hernss/switching_power_supply/TPS54331-KiCad Files/panel/modelos3D/TL2230.stp

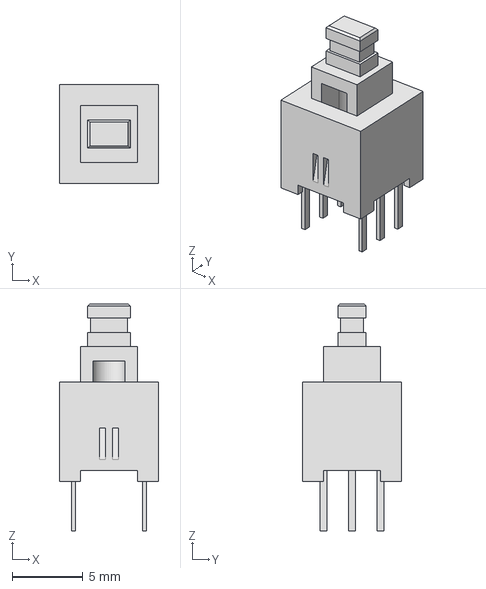
[picture p27: CAD file, 2023-02-13]
TPS54331-KiCad Files/panel/modelos3D/TL2230.stp
7.00 x 7.00 x 16.0 mm
