hernss/switching_power_supply/TPS54331-KiCad Files/modelos3D/srr1260.stp

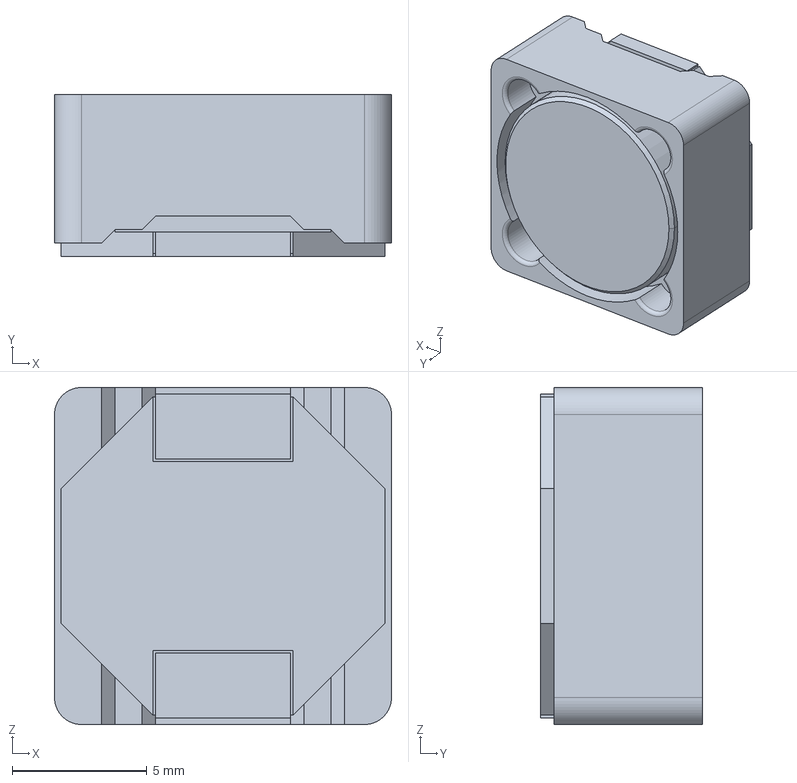
[picture p28: CAD file, 2023-02-13]
TPS54331-KiCad Files/modelos3D/srr1260.stp
12.5 x 6.00 x 12.5 mm
