hernss/switching_power_supply/TPS54331-KiCad Files/modelos3D/Generic POT.step

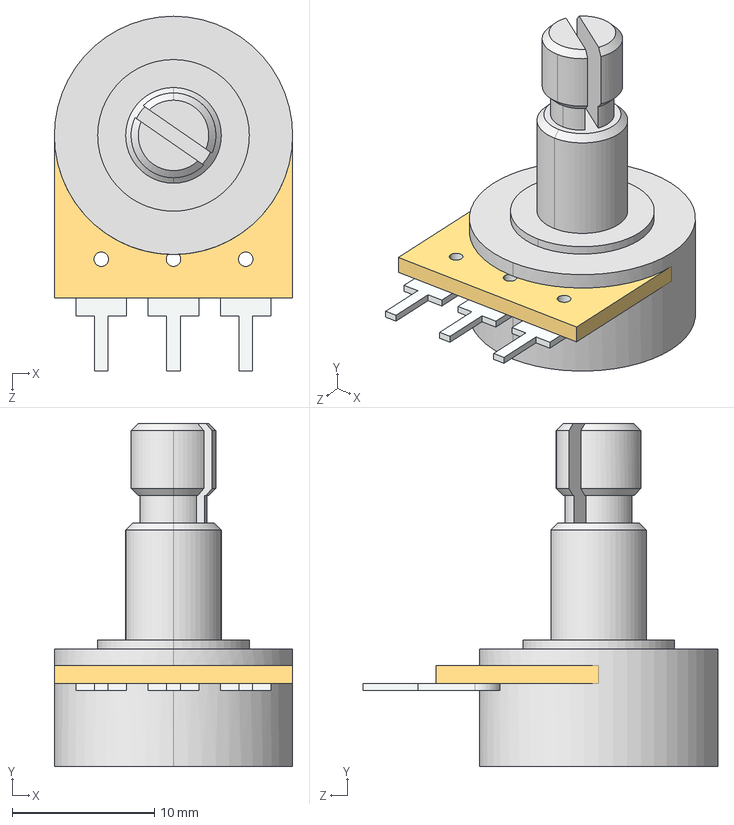
[picture p29: CAD file, 2023-02-13]
TPS54331-KiCad Files/modelos3D/Generic POT.step
16.8 x 24.1 x 24.9 mm
